Anool/STFU_v1/IR_Tx.sch

## KiCad design IR_Tx.sch (2012-07-21)

Schematic: IR_Tx.sch

Parts:
BT1: BATT_Li; CR2032x2
C6: 100n; c_0805
C9: 1n; c_0805
C10: 47n; c_0805
D62: LED; led_5mm_clear
D64: IR_LED; led_5mm_clear
P10: MOD; pin_strip_2
Q2: NPN; to92_2N5401
R5: 10k; R_Var
R6, R41: 120E; r_0805
R7: 15k; r_0805
R42: 47E; r_2512
R43: 220E; r_0805
SW1: SW_STFU; SW-PB; DigiKey P10884S-ND
U6: NE555; SO8E
