Anool/STFU_v1/other_hand.sch

## KiCad design other_hand.sch (2012-07-21)

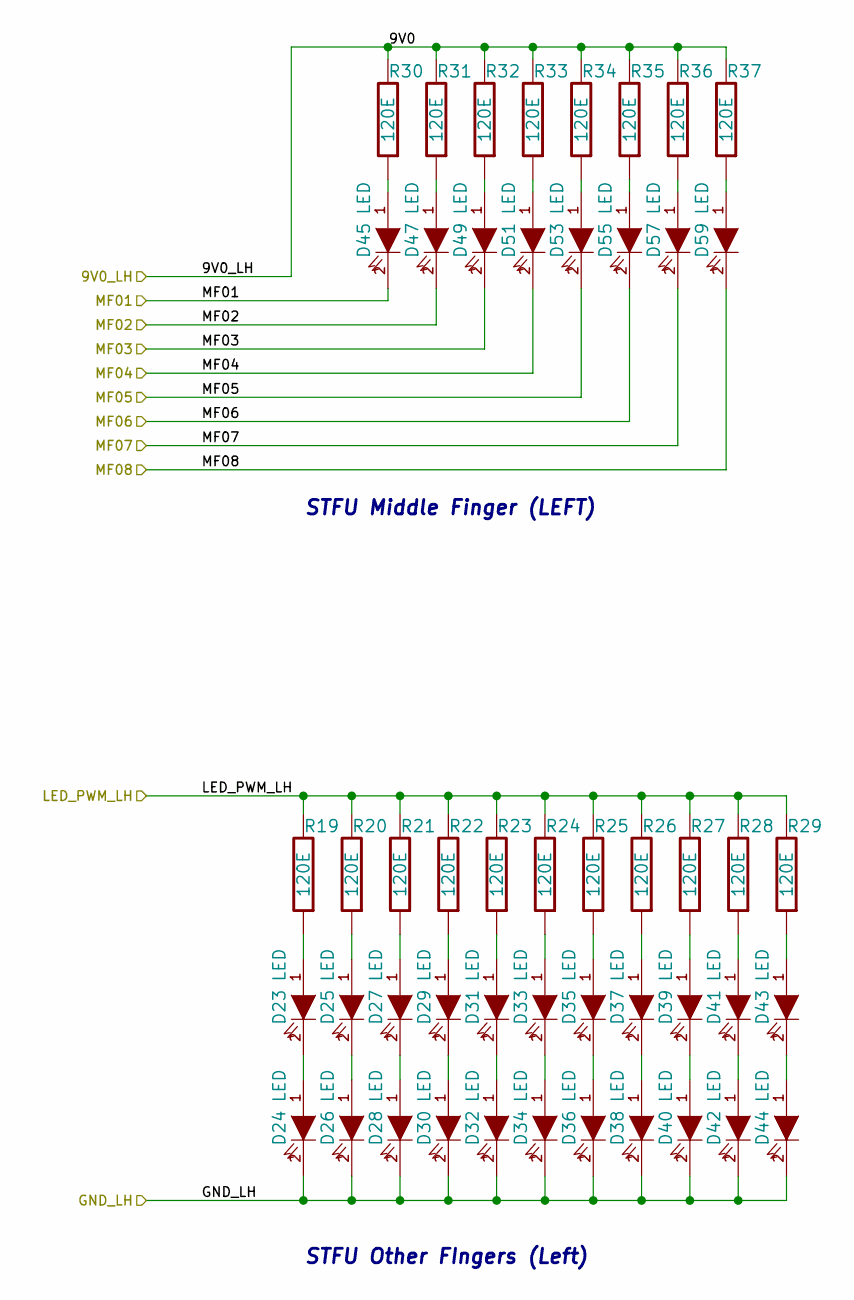
[picture p31: schematic other_hand.sch]

Parts:
D23, D24, D25, D26, D27, D28, D29, D30, D31, D32, D33, D34, D35, D36, D37, D38, D39, D40, D41, D42, D43, D44, D45, D47, D49, D51, D53, D55, D57, D59: LED; d_1206
R19, R20, R21, R22, R23, R24, R25, R26, R27, R28, R29, R30, R31, R32, R33, R34, R35, R36, R37: 120E; r_0805

Connections:
9V0: R30.2, R31.2, R32.2, R33.2, R34.2, R35.2, R36.2, R37.2
GND_LH: D24.2 (K), D26.2 (K), D28.2 (K), D30.2 (K), D32.2 (K), D34.2 (K), D36.2 (K), D38.2 (K), D40.2 (K), D42.2 (K), D44.2 (K)
LED_PWM_LH: R19.2, R20.2, R21.2, R22.2, R23.2, R24.2, R25.2, R26.2, R27.2, R28.2, R29.2
MF01: D45.2 (K)
MF02: D47.2 (K)
MF03: D49.2 (K)
MF04: D51.2 (K)
MF05: D53.2 (K)
MF06: D55.2 (K)
MF07: D57.2 (K)
MF08: D59.2 (K)
unnamed: D23.1 (A), R19.1
unnamed: D23.2 (K), D24.1 (A)
unnamed: D25.1 (A), R20.1
unnamed: D25.2 (K), D26.1 (A)
unnamed: D27.1 (A), R21.1
unnamed: D27.2 (K), D28.1 (A)
unnamed: D29.1 (A), R22.1
unnamed: D29.2 (K), D30.1 (A)
unnamed: D31.1 (A), R23.1
unnamed: D31.2 (K), D32.1 (A)
unnamed: D33.1 (A), R24.1
unnamed: D33.2 (K), D34.1 (A)
unnamed: D35.1 (A), R25.1
unnamed: D35.2 (K), D36.1 (A)
unnamed: D37.1 (A), R26.1
unnamed: D37.2 (K), D38.1 (A)
unnamed: D39.1 (A), R27.1
unnamed: D39.2 (K), D40.1 (A)
unnamed: D41.1 (A), R28.1
unnamed: D41.2 (K), D42.1 (A)
unnamed: D43.1 (A), R29.1
unnamed: D43.2 (K), D44.1 (A)
unnamed: D45.1 (A), R30.1
unnamed: D47.1 (A), R31.1
unnamed: D49.1 (A), R32.1
unnamed: D51.1 (A), R33.1
unnamed: D53.1 (A), R34.1
unnamed: D55.1 (A), R35.1
unnamed: D57.1 (A), R36.1
unnamed: D59.1 (A), R37.1

Notes on the sheet:
STFU Other FIngers (Left)
STFU Middle Finger (LEFT)
