Anool/STFU_v1/stfu.sch

## KiCad design stfu.sch (2012-07-21)

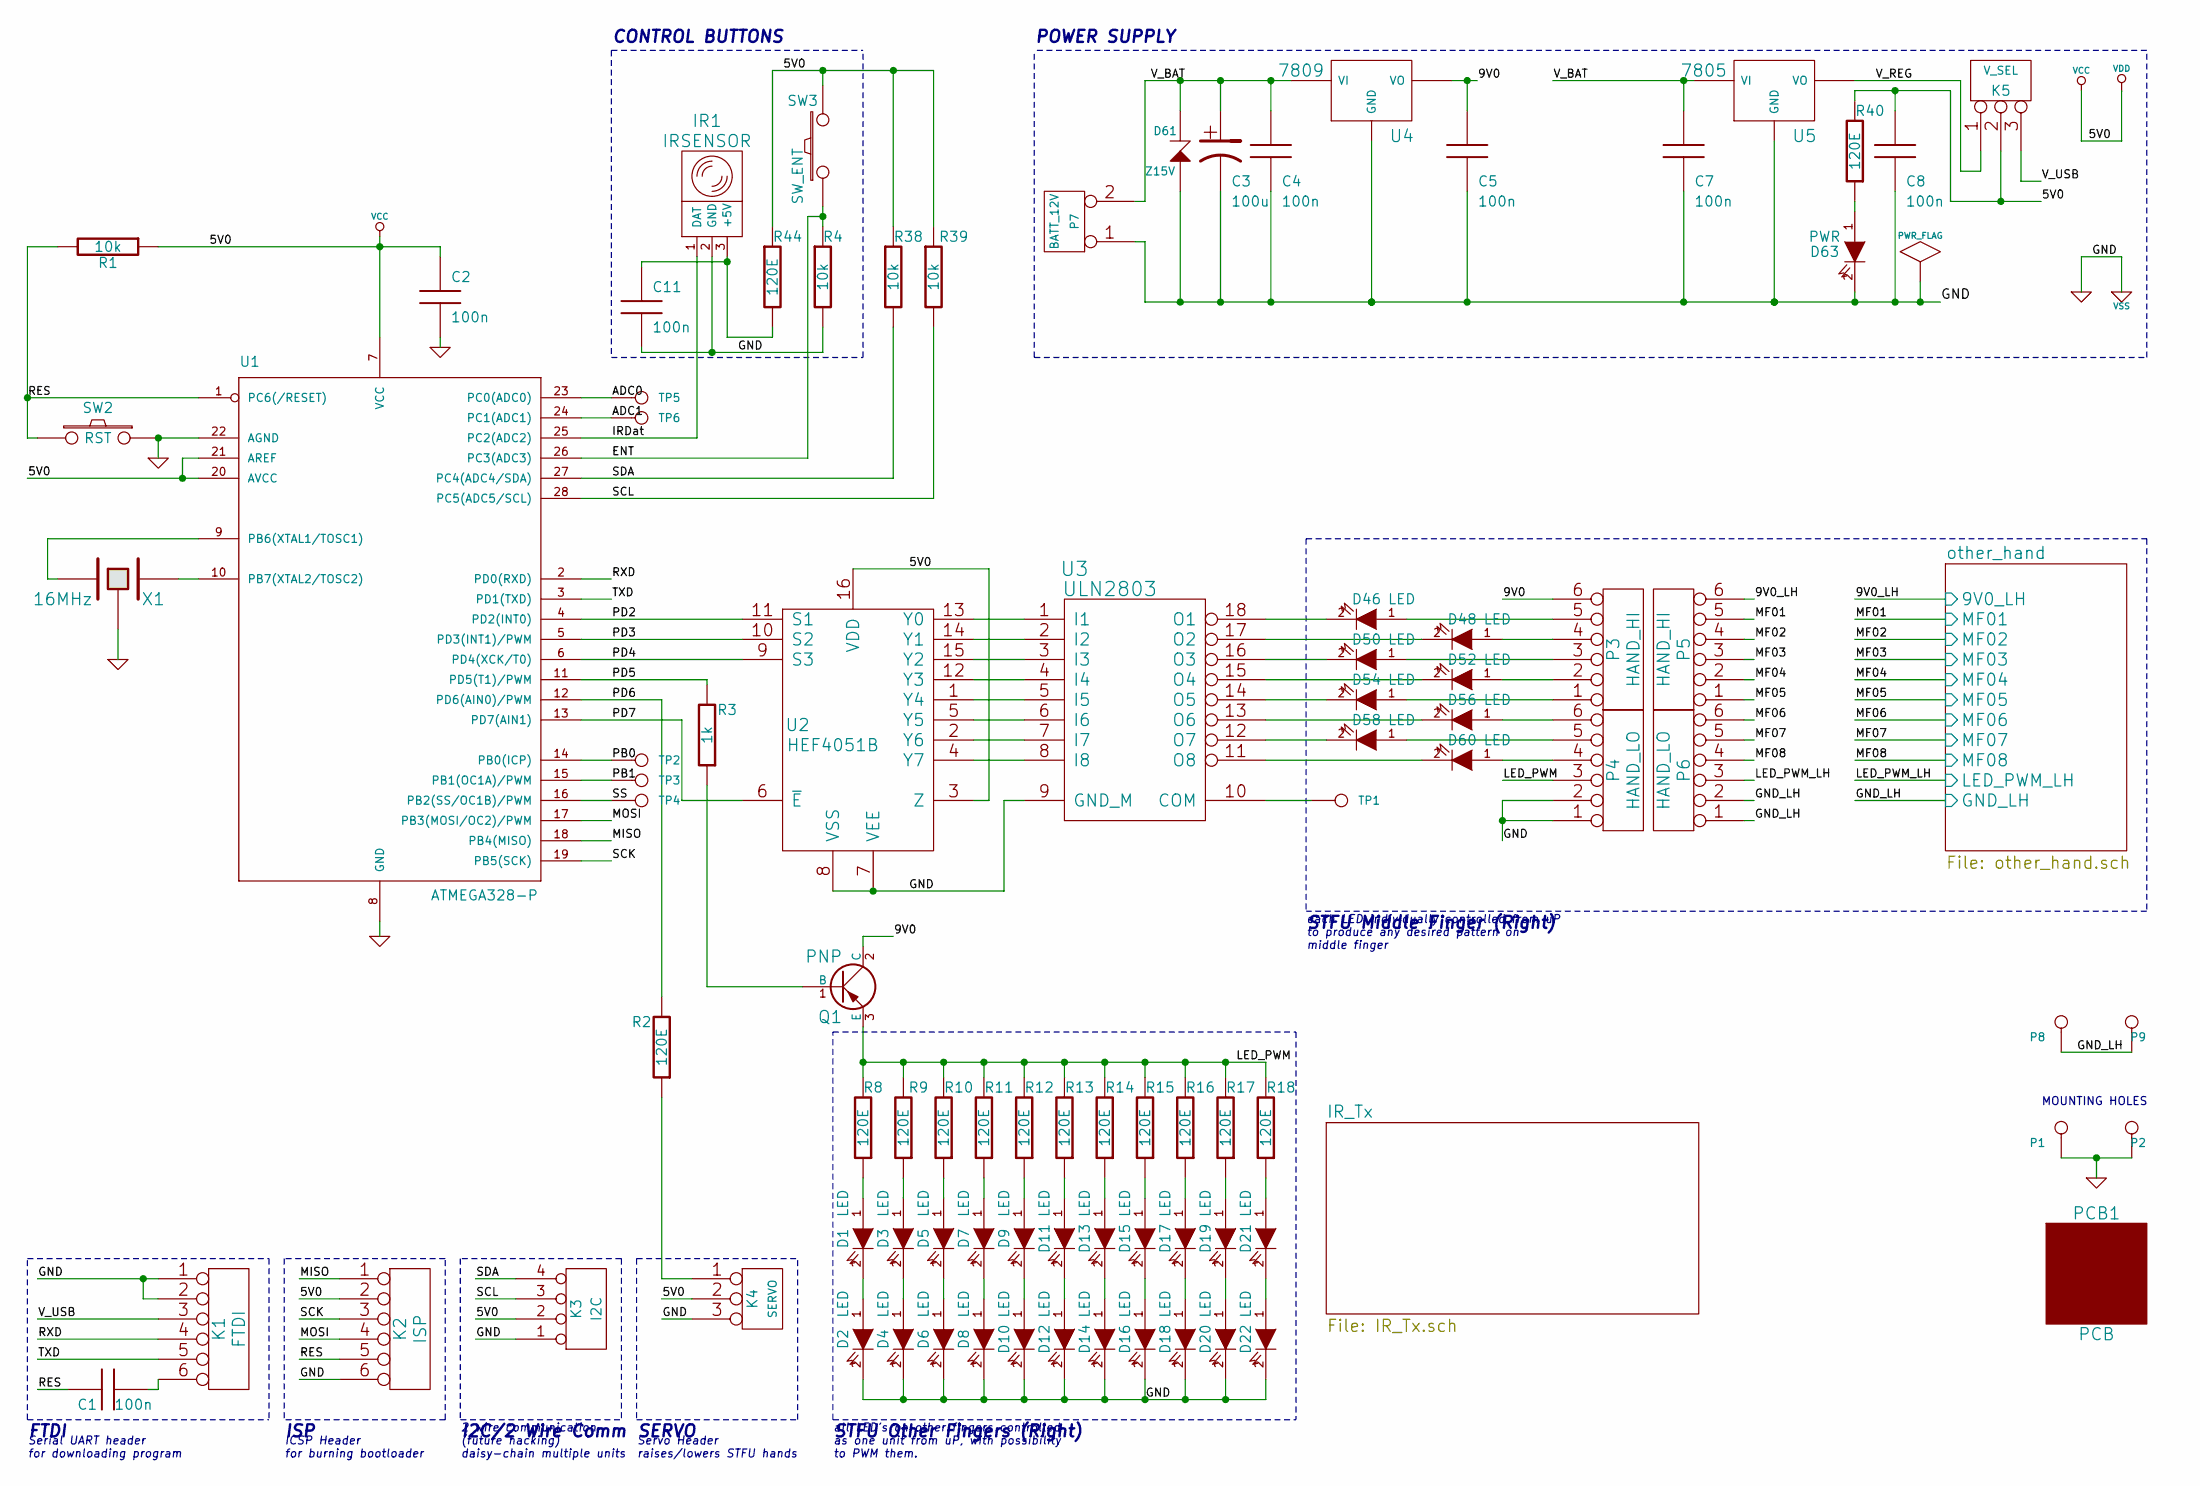
[picture p32: schematic stfu.sch]

Parts:
C1, C2, C4, C5, C7, C8, C11: 100n; c_0805
C3: 100u; C_ELCO_SMD
D1, D2, D3, D4, D5, D6, D7, D8, D9, D10, D11, D12, D13, D14, D15, D16, D17, D18, D19, D20, D21, D22, D46, D48, D50, D52, D54, D56, D58, D60: LED; d_1206
D61: Z15V; SOD323F
D63: PWR; d_0805
IR1: IRSENSOR; pin_strip_3
K1: FTDI; Header_FTDI
K2: ISP; Header_ICSP
K3: I2C; pin_strip_4
K4: SERVO; Header_Ser
K5: V_SEL; Header_V_SEL
P1, P2, P8, P9: CONN_1; vite_3mm
P3, P5: HAND_HI; pin_strip_6b
P4, P6: HAND_LO; pin_strip_6b
P7: BATT_12V; bornier2
PCB1: PCB
Q1: PNP; sot223
R1, R4, R38, R39: 10k; r_0805
R2, R8, R9, R10, R11, R12, R13, R14, R15, R16, R17, R18, R40, R44: 120E; r_0805
R3: 1k; r_0805
SW2: RST; SW_PB_V; DigiKey P10884S-ND
SW3: SW_ENT; SW_PB_V; DigiKey P10884S-ND
TP1, TP2, TP3, TP4, TP5, TP6: CONN_1; I/O
U1: ATMEGA328-P; DIP-28__300_ELL
U2: HEF4051B; SO16E
U3: ULN2803; SO18W
U4: 7809; DPAK-3
U5: 7805; DPAK-3
X1: 16MHz; XTAL; DigiKey 490-1214-ND

Connections:
9V0: C5.1, P3.6, Q1.2 (C), U4.VO
9V0_LH: P5.6
ADC0: TP5.1, U1.23 (PC0(ADC0))
ADC1: TP6.1, U1.24 (PC1(ADC1))
ENT: R4.1, SW3.1, U1.26 (PC3(ADC3))
GND: C2.2, C3.2, C4.2, C5.2, C7.2, C8.2, C11.2, D2.2 (K), D4.2 (K), D6.2 (K), D8.2 (K), D10.2 (K), D12.2 (K), D14.2 (K), D16.2 (K), D18.2 (K), D20.2 (K), D22.2 (K), D61.1 (A), D63.2 (K), IR1.2 (GND), K1.1, K1.2, K2.6, K3.1, K4.3, P1.1, P2.1, P4.1, P4.2, P7.1, R4.2, SW2.1, U1.8 (GND), U1.22 (AGND), U2.7 (VEE), U2.8 (VSS), U3.9 (GND_M), U4.GND, U5.GND, X1.~ (3)
GND_LH: P6.1, P6.2, P8.1, P9.1
IRDat: IR1.1 (DAT), U1.25 (PC2(ADC2))
LED_PWM: P4.3, Q1.3 (E), R8.2, R9.2, R10.2, R11.2, R12.2, R13.2, R14.2, R15.2, R16.2, R17.2, R18.2
LED_PWM_LH: P6.3
MF01: P5.5
MF02: P5.4
MF03: P5.3
MF04: P5.2
MF05: P5.1
MF06: P6.6
MF07: P6.5
MF08: P6.4
MISO: K2.1, U1.18 (PB4(MISO))
MOSI: K2.4, U1.17 (PB3(MOSI/OC2)/PWM)
unnamed: C1.2, K1.6
unnamed: C11.1, IR1.3 (+5V), R44.2
unnamed: D1.1 (A), R8.1
unnamed: D1.2 (K), D2.1 (A)
unnamed: D3.1 (A), R9.1
unnamed: D3.2 (K), D4.1 (A)
unnamed: D5.1 (A), R10.1
unnamed: D5.2 (K), D6.1 (A)
unnamed: D7.1 (A), R11.1
unnamed: D7.2 (K), D8.1 (A)
unnamed: D9.1 (A), R12.1
unnamed: D9.2 (K), D10.1 (A)
unnamed: D11.1 (A), R13.1
unnamed: D11.2 (K), D12.1 (A)
unnamed: D13.1 (A), R14.1
unnamed: D13.2 (K), D14.1 (A)
unnamed: D15.1 (A), R15.1
unnamed: D15.2 (K), D16.1 (A)
unnamed: D17.1 (A), R16.1
unnamed: D17.2 (K), D18.1 (A)
unnamed: D19.1 (A), R17.1
unnamed: D19.2 (K), D20.1 (A)
unnamed: D21.1 (A), R18.1
unnamed: D21.2 (K), D22.1 (A)
unnamed: D46.1 (A), P3.5
unnamed: D46.2 (K), U3.18 (O1)
unnamed: D48.1 (A), P3.4
unnamed: D48.2 (K), U3.17 (O2)
unnamed: D50.1 (A), P3.3
unnamed: D50.2 (K), U3.16 (O3)
unnamed: D52.1 (A), P3.2
unnamed: D52.2 (K), U3.15 (O4)
unnamed: D54.1 (A), P3.1
unnamed: D54.2 (K), U3.14 (O5)
unnamed: D56.1 (A), P4.6
unnamed: D56.2 (K), U3.13 (O6)
unnamed: D58.1 (A), P4.5
unnamed: D58.2 (K), U3.12 (O7)
unnamed: D60.1 (A), P4.4
unnamed: D60.2 (K), U3.11 (O8)
unnamed: D63.1 (A), R40.1
unnamed: K4.1, R2.1
unnamed: Q1.1 (B), R3.1
unnamed: TP1.1, U3.10 (COM)
unnamed: U1.9 (PB6(XTAL1/TOSC1)), X1.1
unnamed: U1.10 (PB7(XTAL2/TOSC2)), X1.2
unnamed: U2.1 (Y4), U3.5 (I5)
unnamed: U2.2 (Y6), U3.7 (I7)
unnamed: U2.4 (Y7), U3.8 (I8)
unnamed: U2.5 (Y5), U3.6 (I6)
unnamed: U2.12 (Y3), U3.4 (I4)
unnamed: U2.13 (Y0), U3.1 (I1)
unnamed: U2.14 (Y1), U3.2 (I2)
unnamed: U2.15 (Y2), U3.3 (I3)
PB0: TP2.1, U1.14 (PB0(ICP))
PB1: TP3.1, U1.15 (PB1(OC1A)/PWM)
PD2: U1.4 (PD2(INT0)), U2.11 (S1)
PD3: U1.5 (PD3(INT1)/PWM), U2.10 (S2)
PD4: U1.6 (PD4(XCK/T0)), U2.9 (S3)
PD5: R3.2, U1.11 (PD5(T1)/PWM)
PD6: R2.2, U1.12 (PD6(AIN0)/PWM)
PD7: U1.13 (PD7(AIN1)), U2.6 (~E)
RES: C1.1, K2.5, R1.2, SW2.2, U1.1 (PC6(/RESET))
RXD: K1.4, U1.2 (PD0(RXD))
SCK: K2.3, U1.19 (PB5(SCK))
SCL: K3.3, R39.2, U1.28 (PC5(ADC5/SCL))
SDA: K3.4, R38.2, U1.27 (PC4(ADC4/SDA))
SS: TP4.1, U1.16 (PB2(SS/OC1B)/PWM)
TXD: K1.5, U1.3 (PD1(TXD))
VCC: C2.1, C8.1, K2.2, K3.2, K4.2 (PM), K5.2 (PM), R1.1, R38.1, R39.1, R40.2, R44.1, SW3.2, U1.7 (VCC), U1.20 (AVCC), U1.21 (AREF), U2.3 (Z), U2.16 (VDD)
V_BAT: C3.1, C4.1, C7.1, D61.2 (K), P7.2 (PM), U4.VI, U5.VI
V_REG: K5.1, U5.VO
V_USB: K1.3, K5.3

Notes on the sheet:
CONTROL BUTTONS
2 wire communication (future hacking) daisy-chain multiple units
Serial UART header for downloading program
ICSP Header for burning bootloader
Servo Header raises/lowers STFU hands
all LED's on other fingers controlled as one unit from uP, with possibility to PWM them.
each LED individually controlled from uP to produce any desired pattern on middle finger
STFU Other Fingers (Right)
STFU Middle Finger (Right)
SERVO
I2C/2 Wire Comm
FTDI
ISP
POWER SUPPLY
MOUNTING HOLES
